TegranGrigorian/EGR227-Final-Project/assets/GUI-state-diagram.drawio.png

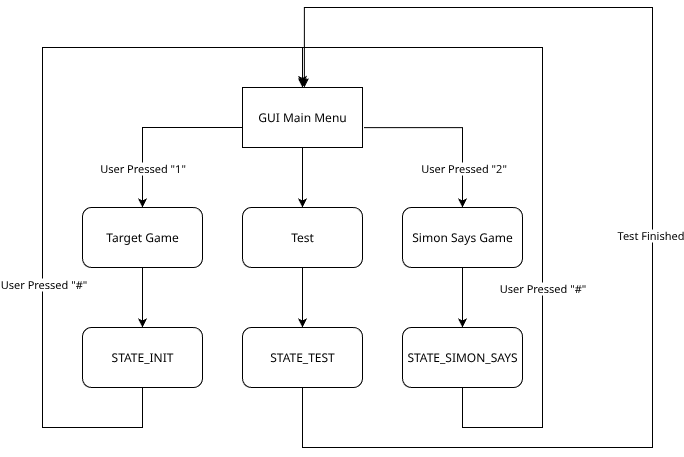
assets/GUI-state-diagram.drawio.png
