TegranGrigorian/EGR227-Final-Project/assets/imgs/20251207_191956.jpg

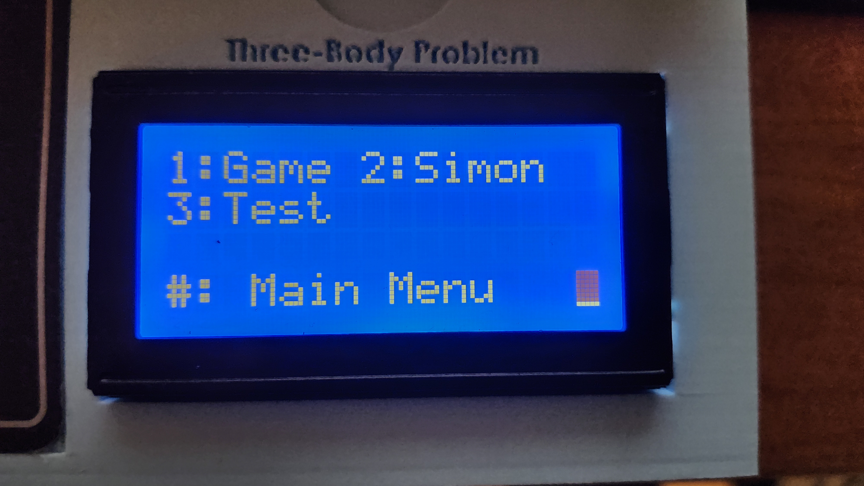
assets/imgs/20251207_191956.jpg
