TegranGrigorian/EGR227-Final-Project/assets/imgs/20251207_192033.jpg

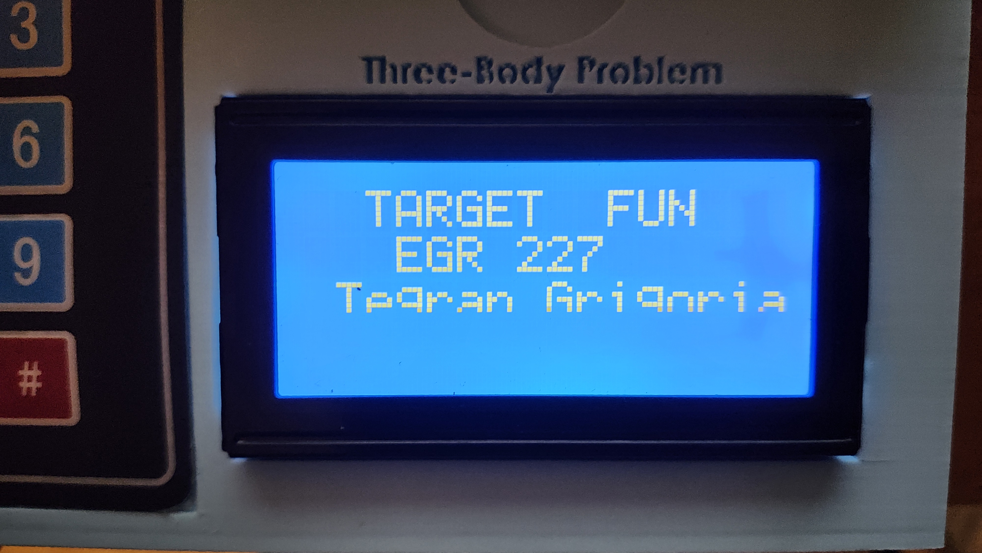
assets/imgs/20251207_192033.jpg
