TegranGrigorian/EGR227-Final-Project/assets/imgs/20251207_192209.jpg

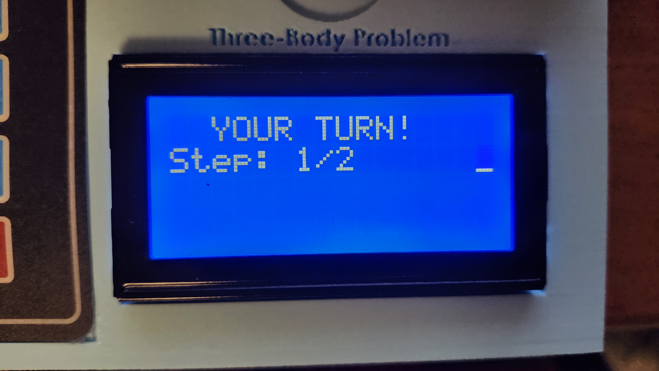
assets/imgs/20251207_192209.jpg
