TegranGrigorian/EGR227-Final-Project/assets/imgs/20251207_192219.jpg

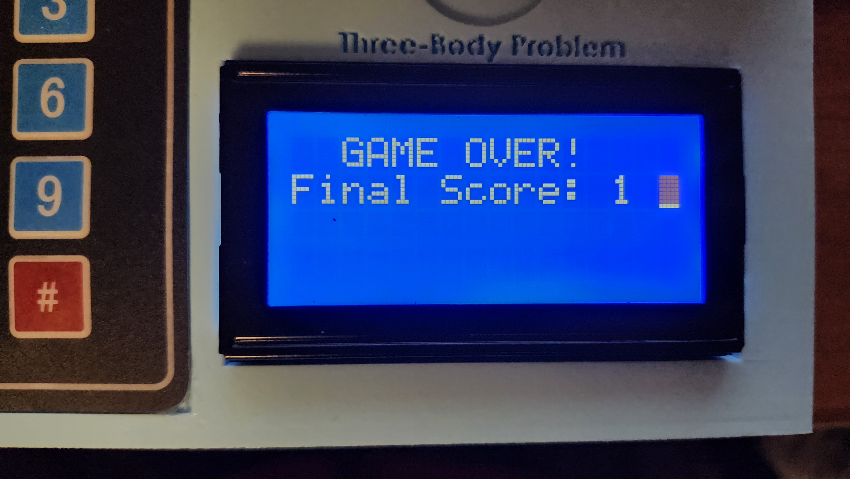
assets/imgs/20251207_192219.jpg
